lutzer/HybridLetterbox/docs/images/programming-attiny44-attiny84-with-arduino-uno.png

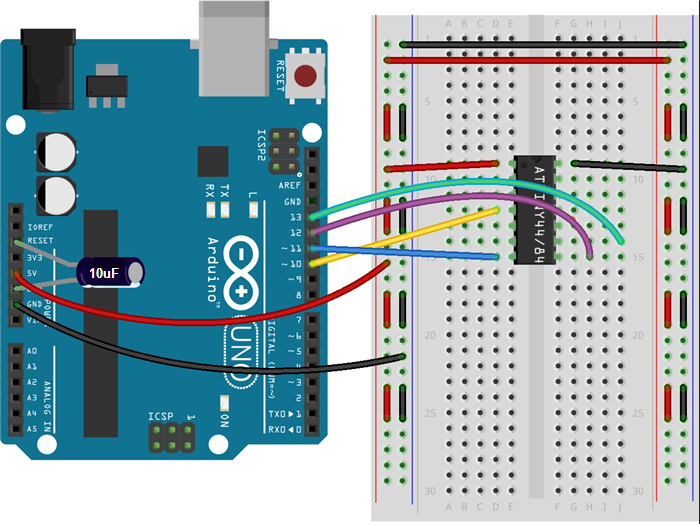
docs/images/programming-attiny44-attiny84-with-arduino-uno.png
