lutzer/HybridLetterbox/resources/hardware/pi_b_plus_layout.jpg

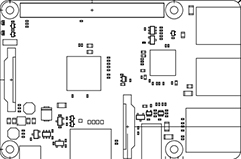
resources/hardware/pi_b_plus_layout.jpg
