lutzer/HybridLetterbox/src/server/www/images/header-img.jpg

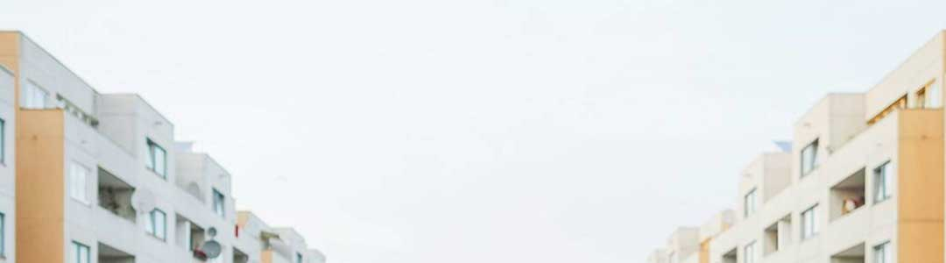
src/server/www/images/header-img.jpg
