lutzer/HybridLetterbox/resources/testscripts/cv/calibration_result.jpg

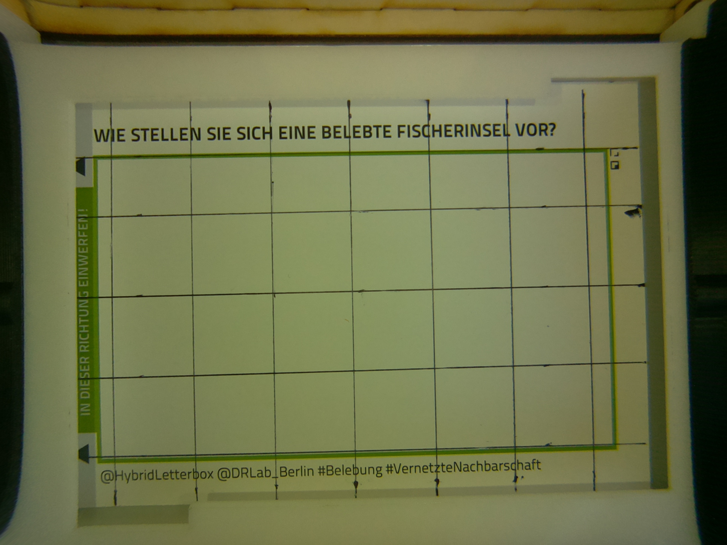
resources/testscripts/cv/calibration_result.jpg
