lutzer/HybridLetterbox/resources/testscripts/cv/images/image1.jpg

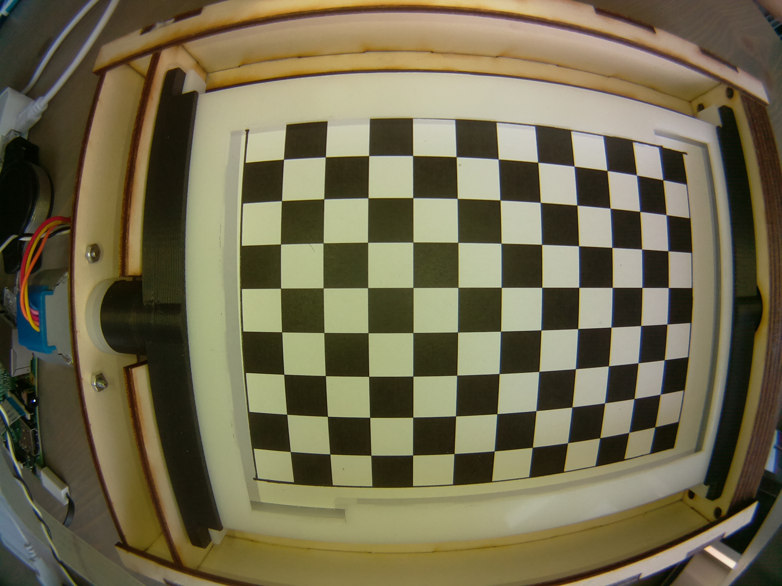
resources/testscripts/cv/images/image1.jpg
