lutzer/HybridLetterbox/resources/testscripts/cv/images/pattern-scan-rotated.jpg

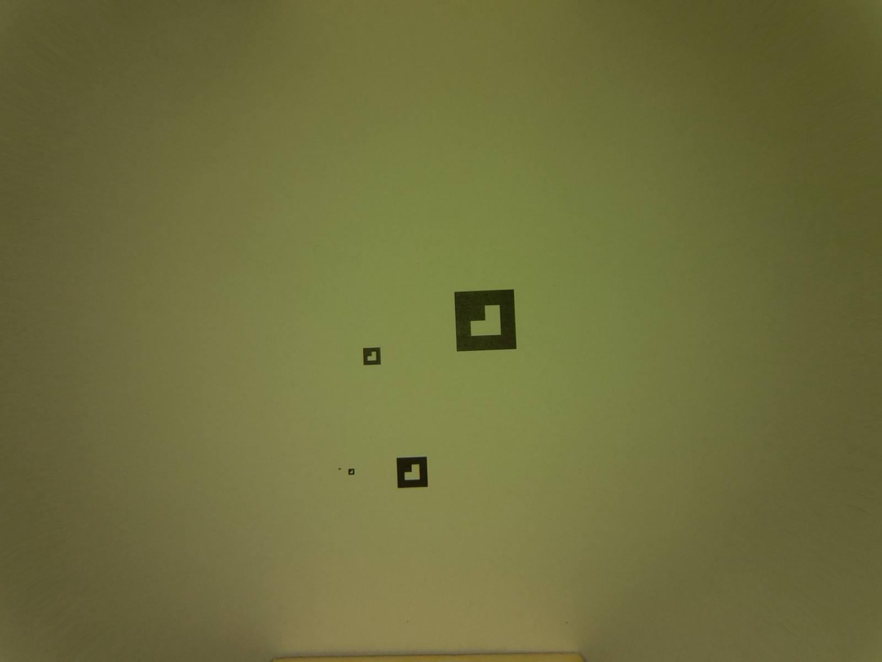
resources/testscripts/cv/images/pattern-scan-rotated.jpg
