lutzer/HybridLetterbox/resources/testscripts/cv/test.jpg

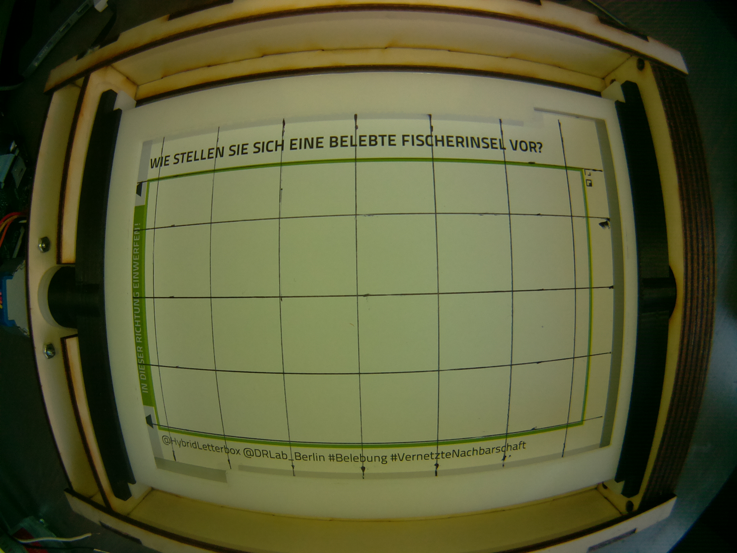
resources/testscripts/cv/test.jpg
