lutzer/HybridLetterbox/resources/testscripts/pi/test123.jpg

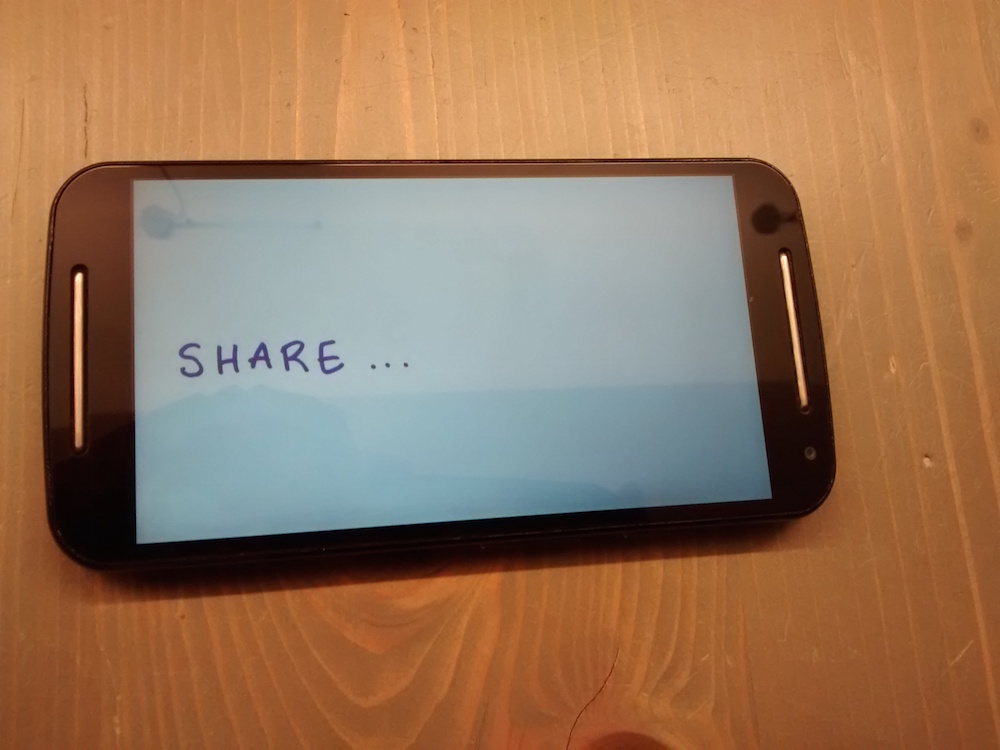
resources/testscripts/pi/test123.jpg
