lutzer/HybridLetterbox/src/server/node/tests/files/img1.jpg

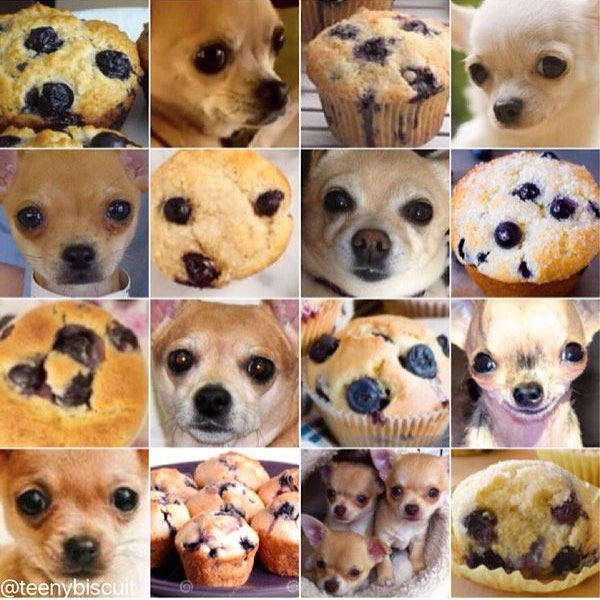
src/server/node/tests/files/img1.jpg
