lutzer/HybridLetterbox/src/server/node/tests/files/img2.jpg

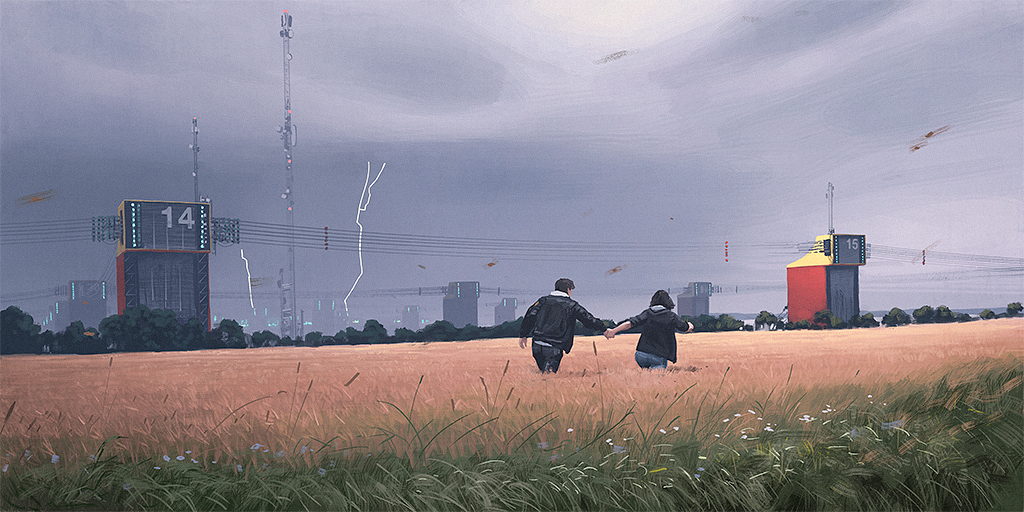
src/server/node/tests/files/img2.jpg
