lutzer/HybridLetterbox/src/server/node/tests/files/img3.jpg

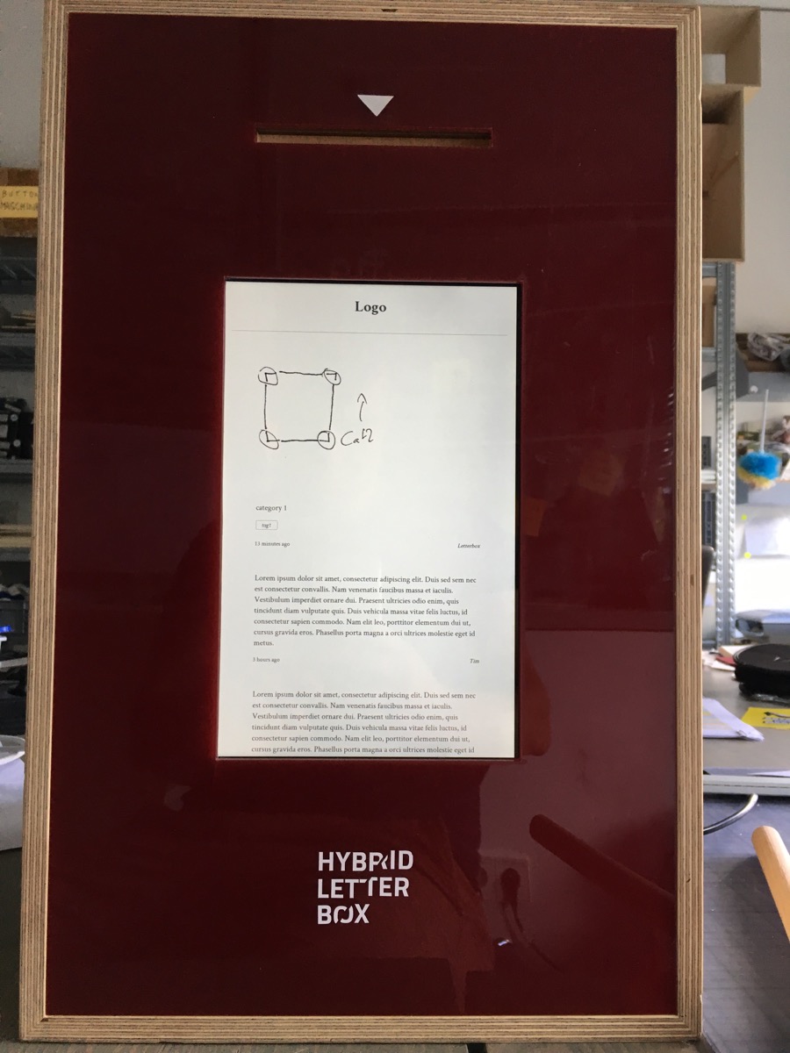
src/server/node/tests/files/img3.jpg
