lutzer/HybridLetterbox/resources/hardware/stepper_board/plots/stepper_board-B.Cu.pdf

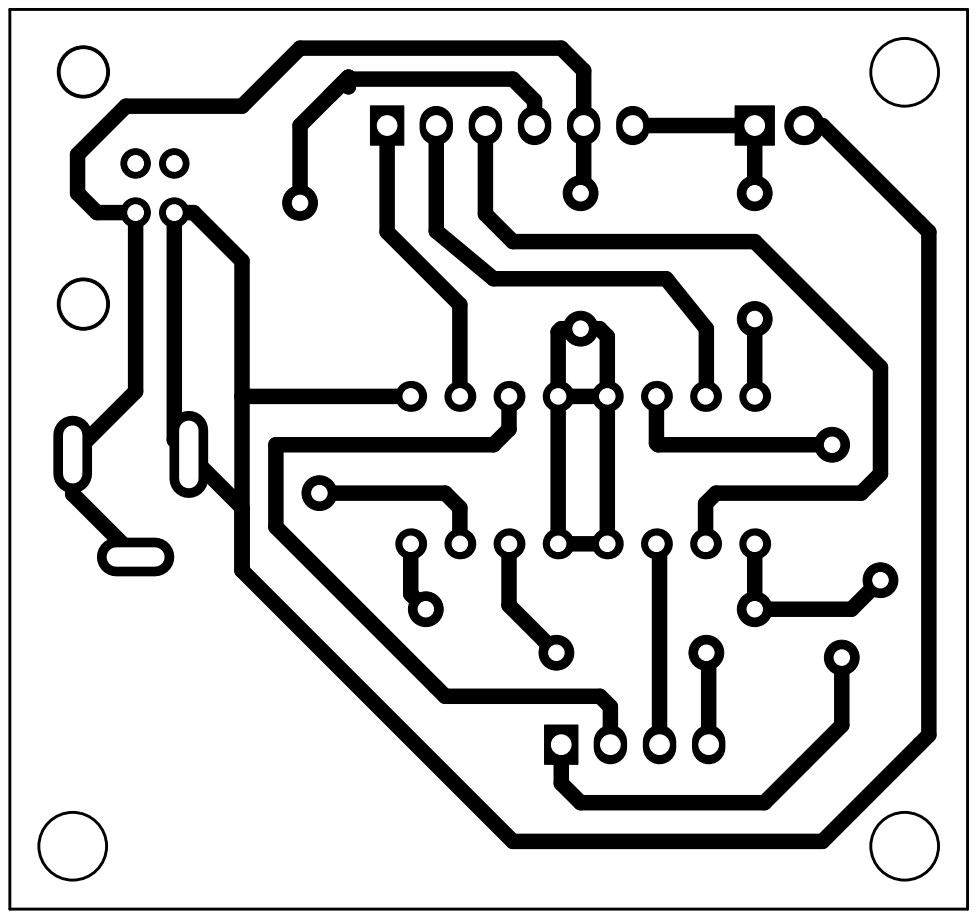
[picture p44: page 1]
