lutzer/HybridLetterbox/resources/hardware/stepper_board/plots/stepper_board-F.Cu.pdf

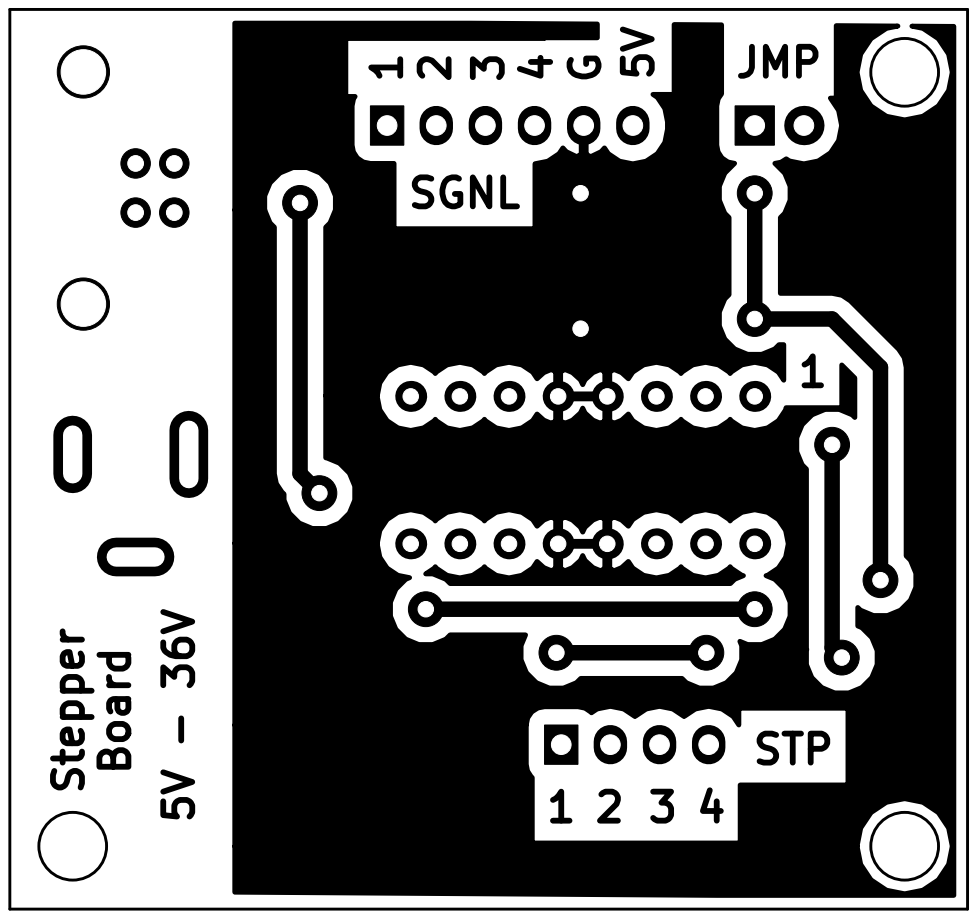
[picture p45: page 1]
